wiki-wolters/vybes/ESP/esp-web-server/websocket.cpp

#include "globals.h"
#include "websocket.h"
#include "web_server.h"
#include "teensy_comm.h"
#include "config.h" // NUM_OUTPUTS, for solo channel validation
#include <ArduinoJson.h>
#include <atomic>

// One handler per listener. esp-idf's httpd runs everything for a server -
// URI handlers (which add websocket clients), session close (which removes
// them) and httpd_queue_work jobs - on that server's single task. Giving
// each listener its own handler and marshaling every broadcast onto the
// owning server's task with httpd_queue_work means a handler's client list
// is only ever touched from one task, so it can never be mutated while a
// broadcast iterates it. (A single handler shared by both listeners - the
// old setup - is unfixable with a mutex on our side: the library mutates
// the list internally on connect/disconnect without taking one.)
PsychicWebSocketHandler wsHttp;
#ifdef CONFIG_IDF_TARGET_ESP32S3
PsychicWebSocketHandler wsHttps;
#endif

// Per-listener client counts, maintained from the handlers' open/close
// callbacks (each runs on its listener's httpd task) and read from the loop
// task to skip work when nobody is connected.
static std::atomic<int> wsHttpClients{0};
static std::atomic<int> wsHttpsClients{0};

static int totalClients() {
    return wsHttpClients.load() + wsHttpsClients.load();
}

// RTA subscription: the analyzer page sends "rta:keepalive" over the socket
// every couple of seconds while it is open. While those keepalives are
// fresh we keep the Teensy's RTA streaming enabled; when they stop (page
// closed, tab hidden, client gone) we turn it off again. The Teensy also
// times out on its own, so a dropped connection can't leave it streaming.
#define RTA_CLIENT_TIMEOUT_MS 5000
#define RTA_TEENSY_REFRESH_MS 2000
static unsigned long rtaLastClientKeepaliveAt = 0;
static bool rtaActive = false;

// GRM (compressor gain-reduction meter) subscription: identical scheme,
// driven by "grm:keepalive" from any page showing the meters.
static unsigned long grmLastClientKeepaliveAt = 0;
static bool grmActive = false;

// VU (input level meter) subscription: identical scheme, driven by
// "vu:keepalive" from any page showing the level bars.
static unsigned long vuLastClientKeepaliveAt = 0;
static bool vuActive = false;

// Output solo subscription: the analyzer sends "solo:<ch>" every couple of
// seconds while it measures one output. Same keepalive scheme; "solo:-1"
// (or any out-of-range channel) drops the interest so the loop clears the
// Teensy's solo immediately instead of waiting for the timeout.
static unsigned long soloLastClientKeepaliveAt = 0;
static int soloChannel = -1;
static bool soloActive = false;

static void setupHandler(PsychicWebSocketHandler &handler, std::atomic<int> &clientCount) {
    handler.onOpen([&clientCount](PsychicWebSocketClient *client) {
        clientCount.fetch_add(1);
        DebugSerial.printf("WebSocket client #%d connected from %s\n",
                           client->socket(), client->remoteIP().toString().c_str());
        // Clients JSON-parse every message, so the greeting must be JSON
        client->sendMessage("{\"type\":\"hello\",\"message\":\"Connected to Vybes\"}");
    });

    handler.onFrame([](PsychicWebSocketRequest *request, httpd_ws_frame *frame) {
        if (frame->type == HTTPD_WS_TYPE_TEXT && frame->len > 0) {
            // frame->payload is not null-terminated - compare with length
            if (frame->len == 13 && strncmp((const char*)frame->payload, "rta:keepalive", 13) == 0) {
                rtaLastClientKeepaliveAt = millis();
                return ESP_OK;
            }
            if (frame->len == 13 && strncmp((const char*)frame->payload, "grm:keepalive", 13) == 0) {
                grmLastClientKeepaliveAt = millis();
                return ESP_OK;
            }
            if (frame->len == 12 && strncmp((const char*)frame->payload, "vu:keepalive", 12) == 0) {
                vuLastClientKeepaliveAt = millis();
                return ESP_OK;
            }
            if (frame->len >= 6 && frame->len <= 8 &&
                strncmp((const char*)frame->payload, "solo:", 5) == 0) {
                char num[4] = {0};
                memcpy(num, frame->payload + 5, frame->len - 5);
                int ch = atoi(num);
                if (ch >= 0 && ch < NUM_OUTPUTS) {
                    soloChannel = ch;
                    soloLastClientKeepaliveAt = millis();
                } else {
                    soloLastClientKeepaliveAt = 0; // explicit clear
                }
                return ESP_OK;
            }
            DebugSerial.printf("WebSocket received: %.*s\n", (int)frame->len, (const char*)frame->payload);
        }
        return ESP_OK;
    });

    handler.onClose([&clientCount](PsychicWebSocketClient *client) {
        clientCount.fetch_sub(1);
        DebugSerial.printf("WebSocket client #%d disconnected\n", client->socket());
    });
}

void setupWebSocket() {
    setupHandler(wsHttp, wsHttpClients);
#ifdef CONFIG_IDF_TARGET_ESP32S3
    setupHandler(wsHttps, wsHttpsClients);
#endif
    DebugSerial.println("WebSocket handlers ready on /live-updates");
}

// A broadcast queued for one listener's httpd task (message copied inline).
struct WsBroadcast {
    PsychicWebSocketHandler *handler;
    char msg[1]; // over-allocated to hold the whole message
};

static void wsBroadcastWork(void *arg) {
    WsBroadcast *b = (WsBroadcast *)arg;
    b->handler->sendAll(b->msg);
    free(b);
}

static void queueBroadcast(PsychicHttpServer &server, PsychicWebSocketHandler &handler,
                           std::atomic<int> &clientCount, const char *message) {
    if (server.server == NULL || clientCount.load() == 0) {
        return; // listener not started, or nobody to tell
    }
    size_t len = strlen(message);
    WsBroadcast *b = (WsBroadcast *)malloc(sizeof(WsBroadcast) + len);
    if (b == NULL) {
        return;
    }
    b->handler = &handler;
    memcpy(b->msg, message, len + 1);
    if (httpd_queue_work(server.server, wsBroadcastWork, b) != ESP_OK) {
        free(b);
    }
}

static void broadcastToAllListeners(const char *message) {
    queueBroadcast(server, wsHttp, wsHttpClients, message);
#ifdef CONFIG_IDF_TARGET_ESP32S3
    queueBroadcast(serverHttps, wsHttps, wsHttpsClients, message);
#endif
}

// Do NOT send WS ping frames from the server: the browser's automatic pong
// is dispatched to PsychicHttp's frame handler (esp-idf only intercepts
// inbound PING/CLOSE itself), whose httpd_ws_recv_frame call errors on
// control frames, and the non-OK return makes esp-idf close the socket.
// Verified against PsychicHttp 1.2.1: every ping killed the connection.

void broadcastWebSocket(const char* message) {
    broadcastToAllListeners(message);
    DebugSerial.print("WebSocket broadcast: ");
    DebugSerial.println(message);
}

// Forward one RTA frame (the hex payload after "RTA ") to all clients.
// Called from teensyCommLoop at ~10Hz, so no debug logging here.
void broadcastRtaFrame(const char* hexData) {
    if (totalClients() == 0) return;
    size_t len = strlen(hexData);
    if (len == 0 || len > 242) return; // up to 121 bands * 2 hex chars
    char buf[272];
    snprintf(buf, sizeof(buf), "{\"type\":\"rta\",\"d\":\"%s\"}", hexData);
    broadcastToAllListeners(buf);
}

// Forward one delay-probe line (the payload after "PROBE ") to all clients
// as a probeEvent message, e.g. {"messageType":"probeEvent","line":"CHIRP 3 2"}.
void broadcastProbeEvent(const char* line) {
    if (totalClients() == 0) return;
    size_t len = strlen(line);
    if (len == 0 || len > 80) return;
    char buf[128];
    snprintf(buf, sizeof(buf), "{\"messageType\":\"probeEvent\",\"line\":\"%s\"}", line);
    broadcastWebSocket(buf);
}

// Tell clients a channel's FIR filter failed to load, so the UI can stop
// presenting that output as corrected when it is running without a filter.
void broadcastFirLoadError(const char* presetName, int output,
                           const char* code, const char* file) {
    if (totalClients() == 0) return;
    if (presetName == nullptr || code == nullptr || file == nullptr) return;
    // Preset names are user-supplied, so serialize rather than snprintf into
    // a JSON template - a quote in a name would otherwise break the message.
    JsonDocument doc;
    doc["messageType"] = "firLoadError";
    doc["presetName"] = presetName;
    doc["output"] = output;
    doc["code"] = code;
    doc["file"] = file;
    String out;
    serializeJson(doc, out);
    broadcastWebSocket(out.c_str());
}

// Full recorder/player snapshot, sent on every Teensy REC STATE line (at
// most 1Hz while a recording or playback runs).
void broadcastRecorderState(const RecorderState& state) {
    if (totalClients() == 0) return;
    JsonDocument doc;
    doc["messageType"] = "recorderState";
    doc["sdPresent"] = state.sdPresent;
    JsonObject rec = doc.createNestedObject("recording");
    rec["active"] = state.recording;
    rec["file"] = state.recordFile;
    rec["seconds"] = state.recordSeconds;
    JsonObject play = doc.createNestedObject("playback");
    play["active"] = state.playing;
    play["file"] = state.playFile;
    play["seconds"] = state.playSeconds;
    play["length"] = state.playLength;
    String out;
    serializeJson(doc, out);
    broadcastWebSocket(out.c_str());
}

void broadcastRecorderError(const char* code, const char* file) {
    if (totalClients() == 0) return;
    JsonDocument doc;
    doc["messageType"] = "recorderError";
    doc["code"] = code;
    doc["file"] = file;
    String out;
    serializeJson(doc, out);
    broadcastWebSocket(out.c_str());
}

void broadcastRecorderWarning(const char* detail) {
    if (totalClients() == 0) return;
    JsonDocument doc;
    doc["messageType"] = "recorderWarning";
    doc["detail"] = detail;
    String out;
    serializeJson(doc, out);
    broadcastWebSocket(out.c_str());
}

void broadcastRecordingsChanged() {
    if (totalClients() == 0) return;
    broadcastWebSocket("{\"messageType\":\"recordingsChanged\"}");
}

// Forward one GRM frame (the hex payload after "GRM ") to all clients.
// Called from teensyCommLoop at ~10Hz while meters are streaming.
void broadcastGrmFrame(const char* hexData) {
    if (totalClients() == 0) return;
    size_t len = strlen(hexData);
    if (len == 0 || len > 6) return; // 3 bands * 2 hex chars
    char buf[48];
    snprintf(buf, sizeof(buf), "{\"type\":\"grm\",\"d\":\"%s\"}", hexData);
    broadcastToAllListeners(buf);
}

// Forward one VU frame (the hex payload after "VU ") to all clients.
// Called from teensyCommLoop at ~20Hz while the level bars are showing.
void broadcastVuFrame(const char* hexData) {
    if (totalClients() == 0) return;
    size_t len = strlen(hexData);
    if (len == 0 || len > 5) return; // 2 peak bytes + 1 clip flag digit
    char buf[48];
    snprintf(buf, sizeof(buf), "{\"type\":\"vu\",\"d\":\"%s\"}", hexData);
    broadcastToAllListeners(buf);
}

// Relay RTA/GRM interest to the Teensy: refresh each keepalive while a web
// client wants frames, send a single stop when interest lapses.
void websocketLoop() {
    unsigned long now = millis();
    bool wantRta = rtaLastClientKeepaliveAt != 0 &&
                   now - rtaLastClientKeepaliveAt < RTA_CLIENT_TIMEOUT_MS &&
                   totalClients() > 0;
    static unsigned long lastTeensyRefreshAt = 0;
    if (wantRta) {
        rtaActive = true;
        if (now - lastTeensyRefreshAt >= RTA_TEENSY_REFRESH_MS) {
            lastTeensyRefreshAt = now;
            sendToTeensy(CMD_SET_RTA, "1");
        }
    } else if (rtaActive) {
        rtaActive = false;
        sendToTeensy(CMD_SET_RTA, "0");
    }

    bool wantGrm = grmLastClientKeepaliveAt != 0 &&
                   now - grmLastClientKeepaliveAt < RTA_CLIENT_TIMEOUT_MS &&
                   totalClients() > 0;
    static unsigned long lastGrmRefreshAt = 0;
    if (wantGrm) {
        grmActive = true;
        if (now - lastGrmRefreshAt >= RTA_TEENSY_REFRESH_MS) {
            lastGrmRefreshAt = now;
            sendToTeensy(CMD_SET_GRM, "1");
        }
    } else if (grmActive) {
        grmActive = false;
        sendToTeensy(CMD_SET_GRM, "0");
    }

    bool wantVu = vuLastClientKeepaliveAt != 0 &&
                  now - vuLastClientKeepaliveAt < RTA_CLIENT_TIMEOUT_MS &&
                  totalClients() > 0;
    static unsigned long lastVuRefreshAt = 0;
    if (wantVu) {
        vuActive = true;
        if (now - lastVuRefreshAt >= RTA_TEENSY_REFRESH_MS) {
            lastVuRefreshAt = now;
            sendToTeensy(CMD_SET_VU, "1");
        }
    } else if (vuActive) {
        vuActive = false;
        sendToTeensy(CMD_SET_VU, "0");
    }

    bool wantSolo = soloLastClientKeepaliveAt != 0 &&
                    now - soloLastClientKeepaliveAt < RTA_CLIENT_TIMEOUT_MS &&
                    totalClients() > 0;
    static unsigned long lastSoloRefreshAt = 0;
    static int lastSentSoloChannel = -1;
    if (wantSolo) {
        soloActive = true;
        // A channel change goes out immediately; otherwise refresh like RTA
        if (soloChannel != lastSentSoloChannel ||
            now - lastSoloRefreshAt >= RTA_TEENSY_REFRESH_MS) {
            lastSoloRefreshAt = now;
            lastSentSoloChannel = soloChannel;
            char chStr[4];
            snprintf(chStr, sizeof(chStr), "%d", soloChannel);
            sendToTeensy(CMD_SOLO_OUTPUT, chStr);
        }
    } else if (soloActive) {
        soloActive = false;
        lastSentSoloChannel = -1;
        sendToTeensy(CMD_SOLO_OUTPUT, "-1");
    }
}
