wiki-wolters/vybes/ESP/esp-web-server/api_system.cpp

#include "globals.h"
#include "config.h"
#include "web_server.h"
#include "websocket.h"
#include "teensy_comm.h"
#include "utilities.h"
#include "api_helpers.h"
#include "health.h"

esp_err_t handleGetStatus(PsychicRequest *request) {
    JsonDocument doc;

    JsonObject speakerGains = doc.createNestedObject("speakerGains");
    speakerGains["left"] = current_config.speakerGains.left * 100.0f;
    speakerGains["right"] = current_config.speakerGains.right * 100.0f;
    speakerGains["sub"] = current_config.speakerGains.sub * 100.0f;
    
    JsonObject inputGains = doc.createNestedObject("inputGains");
    inputGains["spdif"] = current_config.inputGains.spdif;
    inputGains["bluetooth"] = current_config.inputGains.bluetooth;
    inputGains["usb"] = current_config.inputGains.usb;
    inputGains["tone"] = current_config.inputGains.tone;
    inputGains["analog"] = current_config.inputGains.analog;
    inputGains["recorder"] = current_config.inputGains.recorder;
    
    JsonObject mute = doc.createNestedObject("mute");
    mute["muted"] = current_config.muted;
    mute["percent"] = current_config.mutePercent;
    
    JsonObject tone = doc.createNestedObject("tone");
    tone["frequency"] = current_config.toneFrequency;
    tone["volume"] = current_config.toneVolume;
    
    JsonObject noise = doc.createNestedObject("noise");
    noise["volume"] = current_config.noiseVolume;
    
    doc["currentPreset"] = current_config.presets[current_config.active_preset_index].name;
    doc["deviceName"] = current_config.deviceName;

    // Master volume, which lives on the active preset
    doc["volume"] = active_preset().volume;

    // Internal heap headroom - each open TLS socket costs ~40KB, so this is
    // the number to watch when tuning the HTTPS max_open_sockets budget.
    doc["freeHeap"] = ESP.getFreeHeap();

    // Health telemetry. freeHeap above is a spot reading and looks fine right
    // up until the device wedges; these are the numbers that actually predict
    // it. largestFreeBlock is the important one - a TLS handshake needs 16KB
    // contiguous, so once the low-water mark approaches that, HTTPS is dying
    // of fragmentation while freeHeap still reads ~130KB. uptimeMs plus
    // lastRestartCause is how you tell "up for weeks" from "silently
    // restarting every few days".
    JsonObject health = doc.createNestedObject("health");
    health["uptimeMs"] = (uint32_t)millis();
    health["freeInternal"] = healthFreeInternal();
    health["minFreeInternal"] = healthMinFreeInternal();
    health["largestFreeBlock"] = healthLargestFreeBlock();
    health["minLargestFreeBlock"] = healthMinLargestFreeBlock();
    health["resetReason"] = healthResetReasonName();
    health["lastRestartCause"] = healthLastRestartCause();
    // Escalation state: restartStreak counts consecutive watchdog restarts,
    // and degraded means this boot dropped HTTPS to stay reachable at all. A
    // degraded device answers on port 80 only, so the phone's mic features
    // (delay probe, auto-EQ) are down until a healthy uptime clears it.
    // PSRAM carries the TLS record buffers as of 2026-08-24; if these read 0
    // on an S3 build, memory_type did not take and internal heap is exposed
    // again - which is the condition that kept wedging the device.
    health["psramFree"] = healthPsramFree();
    health["psramSize"] = healthPsramSize();
    health["restartStreak"] = healthRestartStreak();
    health["degraded"] = healthDegradedMode();
    // WiFi link quality. Everything above can read clean while the UI still
    // will not load: 2026-09-14 the page crawled at ~4.5KB/s and HTTPS reset
    // partway through, on a device reporting 73 minutes of uptime and 121KB
    // free. The cause was 25% packet loss on the radio, and with no link
    // telemetry here it took pinging the device against another host on the
    // same AP to see it. minRssi is the one to read - rssi alone swings
    // several dB between samples - and wifiChannel is what to weigh against
    // the neighbours, this silicon being 2.4GHz only. All three read 0 in
    // standalone AP mode, which has no upstream link to measure.
    health["rssi"] = healthRssi();
    health["minRssi"] = healthMinRssi();
    health["wifiChannel"] = healthWifiChannel();

    String response;
    serializeJson(doc, response);
    return request->reply(200, "application/json", response.c_str());
}

// PUT /device/name?name= - rename the device so several Vybes units can
// share one network. Applies to mDNS immediately; the standalone-AP SSID
// and setup-portal name pick it up on the next boot. The TLS certificate
// must be re-issued for the new hostname (ESP/make-certs.sh <name>.local)
// or HTTPS clients will see a name mismatch.
esp_err_t handlePutDeviceName(PsychicRequest *request) {
    if (!request->hasParam("name")) {
        return request->reply(400, "text/plain", "Missing name parameter");
    }
    String name = request->getParam("name")->value();

    if (!is_valid_device_name(name.c_str())) {
        return request->reply(400, "text/plain",
            "Device name must be 1-24 characters of lowercase letters, digits and dashes, not starting or ending with a dash");
    }

    {
        ConfigLock lock;
        strlcpy(current_config.deviceName, name.c_str(), sizeof(current_config.deviceName));
        scheduleConfigWrite();
    }

    // Re-announce "<name>.local" right away
    startMdns();

    JsonDocument doc;
    doc["messageType"] = "deviceNameChanged";
    doc["deviceName"] = current_config.deviceName;
    return sendJsonAndBroadcast(request, doc);
}

esp_err_t handlePutMute(PsychicRequest *request) {
    if (!request->hasParam("state")) {
        return request->reply(400, "text/plain", "Missing required parameters");
    }
    String state = request->getParam("state")->value();
    
    DebugSerial.print("Put Mute: ");DebugSerial.println(state);

    if (state != "on" && state != "off") {
        return request->reply(400, "text/plain", "Invalid state");
    }

    {
        ConfigLock lock;
        current_config.muted = (state == "on");
        scheduleConfigWrite();
    }

    sendOnOffToTeensy(CMD_SET_MUTE, current_config.muted);

    // Same shape as the broadcast sent by toggle_mute (IR remote path)
    JsonDocument doc;
    doc["messageType"] = "muteChanged";
    doc["muted"] = current_config.muted;
    return sendJsonAndBroadcast(request, doc);
}

esp_err_t handlePutMutePercent(PsychicRequest *request) {
    if (!request->hasParam("percent")) {
        return request->reply(400, "text/plain", "Missing required parameters");
    }
    String percentStr = request->getParam("percent")->value();
    int percent = percentStr.toInt();

    if (percent < 0 || percent > 100) {
        return request->reply(400, "text/plain", "Invalid percent value");
    }

    {
        ConfigLock lock;
        current_config.mutePercent = percent;
        scheduleConfigWrite();
    }

    sendFloatToTeensy(CMD_SET_MUTE_PERCENT, percent);

    JsonDocument doc;
    doc["messageType"] = "mutePercentChanged";
    doc["mutePercent"] = current_config.mutePercent;
    return sendJsonAndBroadcast(request, doc);
}
