wiki-wolters/vybes/Teensy/fir_filters/FirEngine.h

#ifndef FIR_ENGINE_H
#define FIR_ENGINE_H

#include <stdint.h>
#include <arm_math.h>

#include "CoeffSource.h"

// Hardware-free core of the FIR filter, with two interchangeable engines:
//
//  - Direct form: CMSIS arm_fir_f32. Cost grows linearly with tap count, so
//    three channels max out the CPU around 2000 taps.
//
//  - Fast convolution: uniformly partitioned overlap-save. The filter is
//    split into 128-tap partitions, each pre-transformed with a 256-point
//    real FFT at load time. Per audio block the input is FFT'd once and
//    multiplied against every partition through a frequency-domain delay
//    line, so cost grows only slightly with tap count. Output is sample
//    identical to the direct engine (no added latency).
//
// The engine is chosen with setFastConvolution() and takes effect at the
// next coefficient load. This class has no AudioStream/Arduino dependencies
// so it can be exercised host-side; AudioFilterFIRFloat wraps it into the
// Teensy audio graph.
#ifdef VYBES_FIR_PROFILE
// Per-stage cycle accounting for the fast engine, compiled only into the
// bench env (see Teensy/fir_bench). Production builds carry none of this.
extern uint64_t firProfFwd, firProfMac, firProfInv, firProfBlocks;
#endif

class FirEngine {

public:
  static const uint16_t BLOCK_SAMPLES = 128;
  static const uint16_t FFT_SIZE = BLOCK_SAMPLES * 2;

  FirEngine();

  // Destructor to free allocated memory
  ~FirEngine();

  // Select the engine used by the next coefficient load
  void setFastConvolution(bool enable);

  // Load new FIR coefficients (the engine keeps its own copy). Returns false
  // if buffer allocation failed (the previous filter stays loaded). This is
  // buildPending() + swapPending() + freeRetired() in one call; callers that
  // process audio from an interrupt should use the three phases directly so
  // only the pointer swap runs inside their critical section.
  bool loadCoefficients(const float* coeffs, uint16_t numTaps);

  // Same, pulling the coefficients from a feed instead of a finished array.
  // Prefer this for anything loaded off the SD card: the engine consumes one
  // partition at a time, so the filter never exists in RAM outside the
  // buffers below (see CoeffFeed). Also returns false if the feed comes up
  // short, which the caller must distinguish from an allocation failure.
  bool loadCoefficients(CoeffFeed& feed, uint16_t numTaps);

  // Three-phase coefficient load:
  //  1. buildPending: allocate and pre-transform the new engine buffers
  //     (slow; run with interrupts enabled). Returns false on allocation
  //     failure, in which case nothing is pending and the current filter
  //     is untouched.
  //  2. swapPending: swap the pending buffers in and re-initialize the
  //     filter (fast pointer swap; run with interrupts disabled).
  //  3. freeRetired: release the replaced buffers (run with interrupts
  //     enabled).
  bool buildPending(const float* coeffs, uint16_t numTaps);
  bool buildPending(CoeffFeed& feed, uint16_t numTaps);

  // buildPending split in two, for a caller loading several filters in one
  // go. Reserve every filter's buffers back-to-back first, then fill them:
  // the partition arrays are large and need contiguous runs, and anything
  // that allocates in between (an SD open, a String temporary) cuts the free
  // space into pieces too small to serve the next one. reservePending
  // allocates and nothing else; fillPending reads the coefficients in and
  // makes the reservation swappable; discardPending releases a reservation
  // that will not be filled. A failed fill discards its own reservation.
  bool reservePending(uint16_t numTaps);
  bool fillPending(CoeffFeed& feed);
  void discardPending();

  // Floats a reservation for numTaps needs, so a caller can size one block
  // for a whole set of filters.
  size_t pendingFloats(uint16_t numTaps) const;

  // reservePending against caller-supplied storage - pendingFloats(numTaps)
  // floats, which the engine reads and writes but never frees. One block
  // sliced across every filter costs the allocator's per-request padding
  // once instead of once per filter; at the pool limit that padding was the
  // difference between the set fitting and the last filter failing.
  // The storage must outlive the filter, i.e. until the next load replaces
  // it - clear the filters before releasing it.
  bool reservePendingIn(float* storage, uint16_t numTaps);

  void swapPending();
  void freeRetired();

  // Process one BLOCK_SAMPLES-sample block through the loaded filter. With
  // no filter loaded (taps() == 0) the input is copied through unchanged,
  // matching the wrapper's bypass semantics.
  void processBlock(const float* input, float* output);

  // Restart the fast-convolution history from silence. Called after a gap in
  // processing (bypassed, upstream stalled) so stale audio isn't convolved.
  void resetHistory();

  uint16_t taps() const { return numTaps; }
  bool fastLoaded() const { return loadedFast; }

private:
  void processDirect(const float* input, float* output);
  void processFast(const float* input, float* output);

  // One engine's worth of coefficient/state buffers, so the pending and
  // retired sets can be carried between the load phases.
  struct Buffers {
    float* coeffs;       // direct: FIR coefficients
    float* state;        // direct: FIR state buffer
    float* partSpectra;  // fast: numPartitions x FFT_SIZE filter partition spectra
    float* fdl;          // fast: numPartitions x FFT_SIZE input spectra history
    uint16_t partitions;
    uint16_t taps;
    bool fast;
    bool owned;          // false when the storage belongs to the caller
  };

  // Direct engine
  arm_fir_instance_f32 fir;
  float* firCoeffs;      // FIR coefficients (OWNED by this class)
  float* firState;       // FIR state buffer (OWNED by this class)

  // Fast convolution engine
  arm_rfft_fast_instance_f32 rfft;      // read-only after construction
  float* partSpectra;    // numPartitions x FFT_SIZE filter partition spectra (OWNED)
  float* fdl;            // numPartitions x FFT_SIZE input spectra history (OWNED)
  float prevBlock[BLOCK_SAMPLES]; // previous input block (overlap-save)
  uint16_t numPartitions;
  uint16_t fdlIndex;     // frequency-domain delay line slot of the newest block

  uint16_t numTaps;
  bool useFastConvolution; // engine for the next coefficient load
  bool loadedFast;         // engine the current coefficients were built for
  bool loadedOwned;        // whether the current buffers are ours to free

  Buffers pending;         // built by buildPending, consumed by swapPending
  Buffers retired;         // produced by swapPending, freed by freeRetired
  bool pendingReserved;    // pending holds buffers (filled or not)
  bool pendingValid;       // pending is filled and ready to swap
};

#endif // FIR_ENGINE_H
