wiki-wolters/vybes/ESP/esp-web-server/button.cpp

#include "globals.h"
#include "button.h"
#include "config.h"
#include "screen.h"
#include "websocket.h"
#include "utilities.h"
#include "teensy_comm.h"
#include <Wire.h>
#include <ArduinoJson.h>
#include <string.h>

#include "board_pins.h"

const int BUTTON_PIN = PIN_BUTTON;
const int BLUETOOTH_PAIRING_PIN = PIN_BT_PAIRING; // output to the BT module's pair pin

unsigned long pressStart = 0;
String lastMessage = "";
unsigned long lastButtonPressTime = 0;
int8_t currentPresetIndex = 0;

// Add function to check if backlight is on
extern unsigned long backlightStart; // Need to access this from screen.cpp
extern LiquidCrystal_PCF8574 lcd;    // Need to access LCD object

bool isBacklightOn() {
    return backlightStart > 0;
}

void setupButton() {
    pinMode(BUTTON_PIN, INPUT_PULLUP);
    pinMode(BLUETOOTH_PAIRING_PIN, OUTPUT);
    digitalWrite(BLUETOOTH_PAIRING_PIN, LOW);
    currentPresetIndex = current_config.active_preset_index;
}

unsigned long lastButtonScreenUpdateTime = 0;
const unsigned long BUTTON_SCREEN_UPDATE_INTERVAL = 200; // milliseconds

void nextPreset() {
    // Advance to the next in-use slot, skipping holes left by deleted
    // presets. Bounded so an all-empty table can't hang the loop task.
    int index = currentPresetIndex;
    for (int i = 0; i < MAX_PRESETS; i++) {
        index = (index + 1) % MAX_PRESETS;
        if (strlen(current_config.presets[index].name) > 0) {
            currentPresetIndex = index;
            break;
        }
    }
    lastButtonPressTime = millis();
}

void handleShortPress() {
    // Check if backlight is off
    if (!isBacklightOn()) {
        // Just turn on backlight and show current preset
        lcd.setBacklight(1);
        backlightStart = millis();
        if (millis() - lastButtonScreenUpdateTime > BUTTON_SCREEN_UPDATE_INTERVAL) {
            writeToScreen(current_config.presets[currentPresetIndex].name);
            lastButtonScreenUpdateTime = millis();
        }
    } else {
        // Preset switching is locked while a recording runs (a switch's FIR
        // load would glitch it) - show why instead of cycling
        if (isRecordingActive()) {
            writeToScreen("Presets locked\nwhile recording", 2000);
            return;
        }
        // Backlight is on, so cycle to next preset
        nextPreset(); // Update the preset index
        if (millis() - lastButtonScreenUpdateTime > BUTTON_SCREEN_UPDATE_INTERVAL) {
            writeToScreen(current_config.presets[currentPresetIndex].name); // Display the new preset
            lastButtonScreenUpdateTime = millis();
        }
    }
}
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
